normanwink/Lily58-Glow-Enc/firmware/lily58/keymaps/orvisevans/config.h

/*
This is the c configuration file for the keymap

Copyright 2012 Jun Wako <wakojun@gmail.com>
Copyright 2015 Jack Humbert

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
You should have received a copy of the GNU General Public License
along with this program.  If not, see <http://www.gnu.org/licenses/>.
*/

#pragma once

//#define USE_MATRIX_I2C

/* Select hand configuration */

#define MASTER_LEFT

#define USE_SERIAL_PD2

#define TAPPING_FORCE_HOLD
#define TAPPING_TERM 100
